CIRCUITSTATE/AQEYE-SB-D1/Export/R0.1/2025-06-06/Renders/AQEYE-SB-D1-R0.1-PCB-Left-06062025-1.png

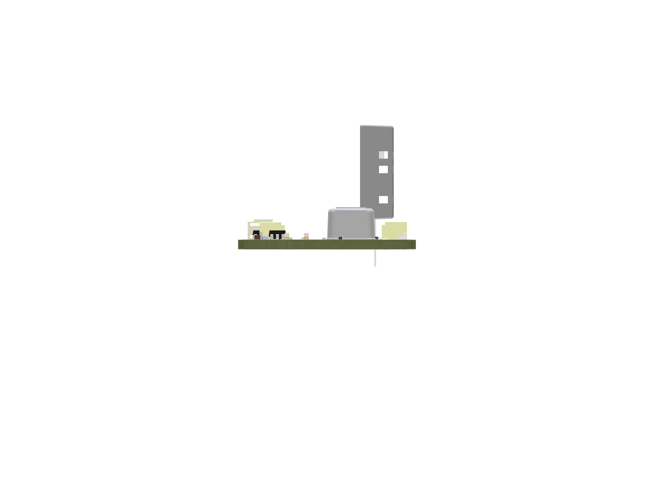
Export/R0.1/2025-06-06/Renders/AQEYE-SB-D1-R0.1-PCB-Left-06062025-1.png
