CIRCUITSTATE/AQEYE-SB-D1/References/sensors_SGP40_sch.png

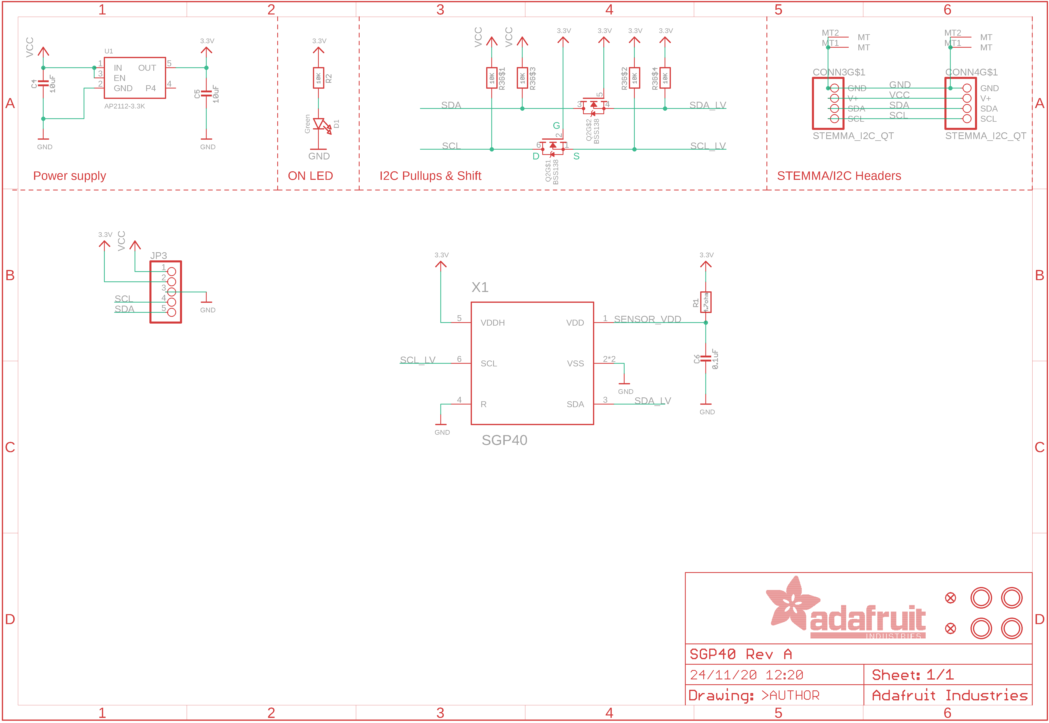
References/sensors_SGP40_sch.png
