CIRCUITSTATE/AQEYE-SB-D1/Export/R0.1/2025-06-08/SCH/AQEYE-SB-D1-R0.1-SCH-08062025-1.pdf

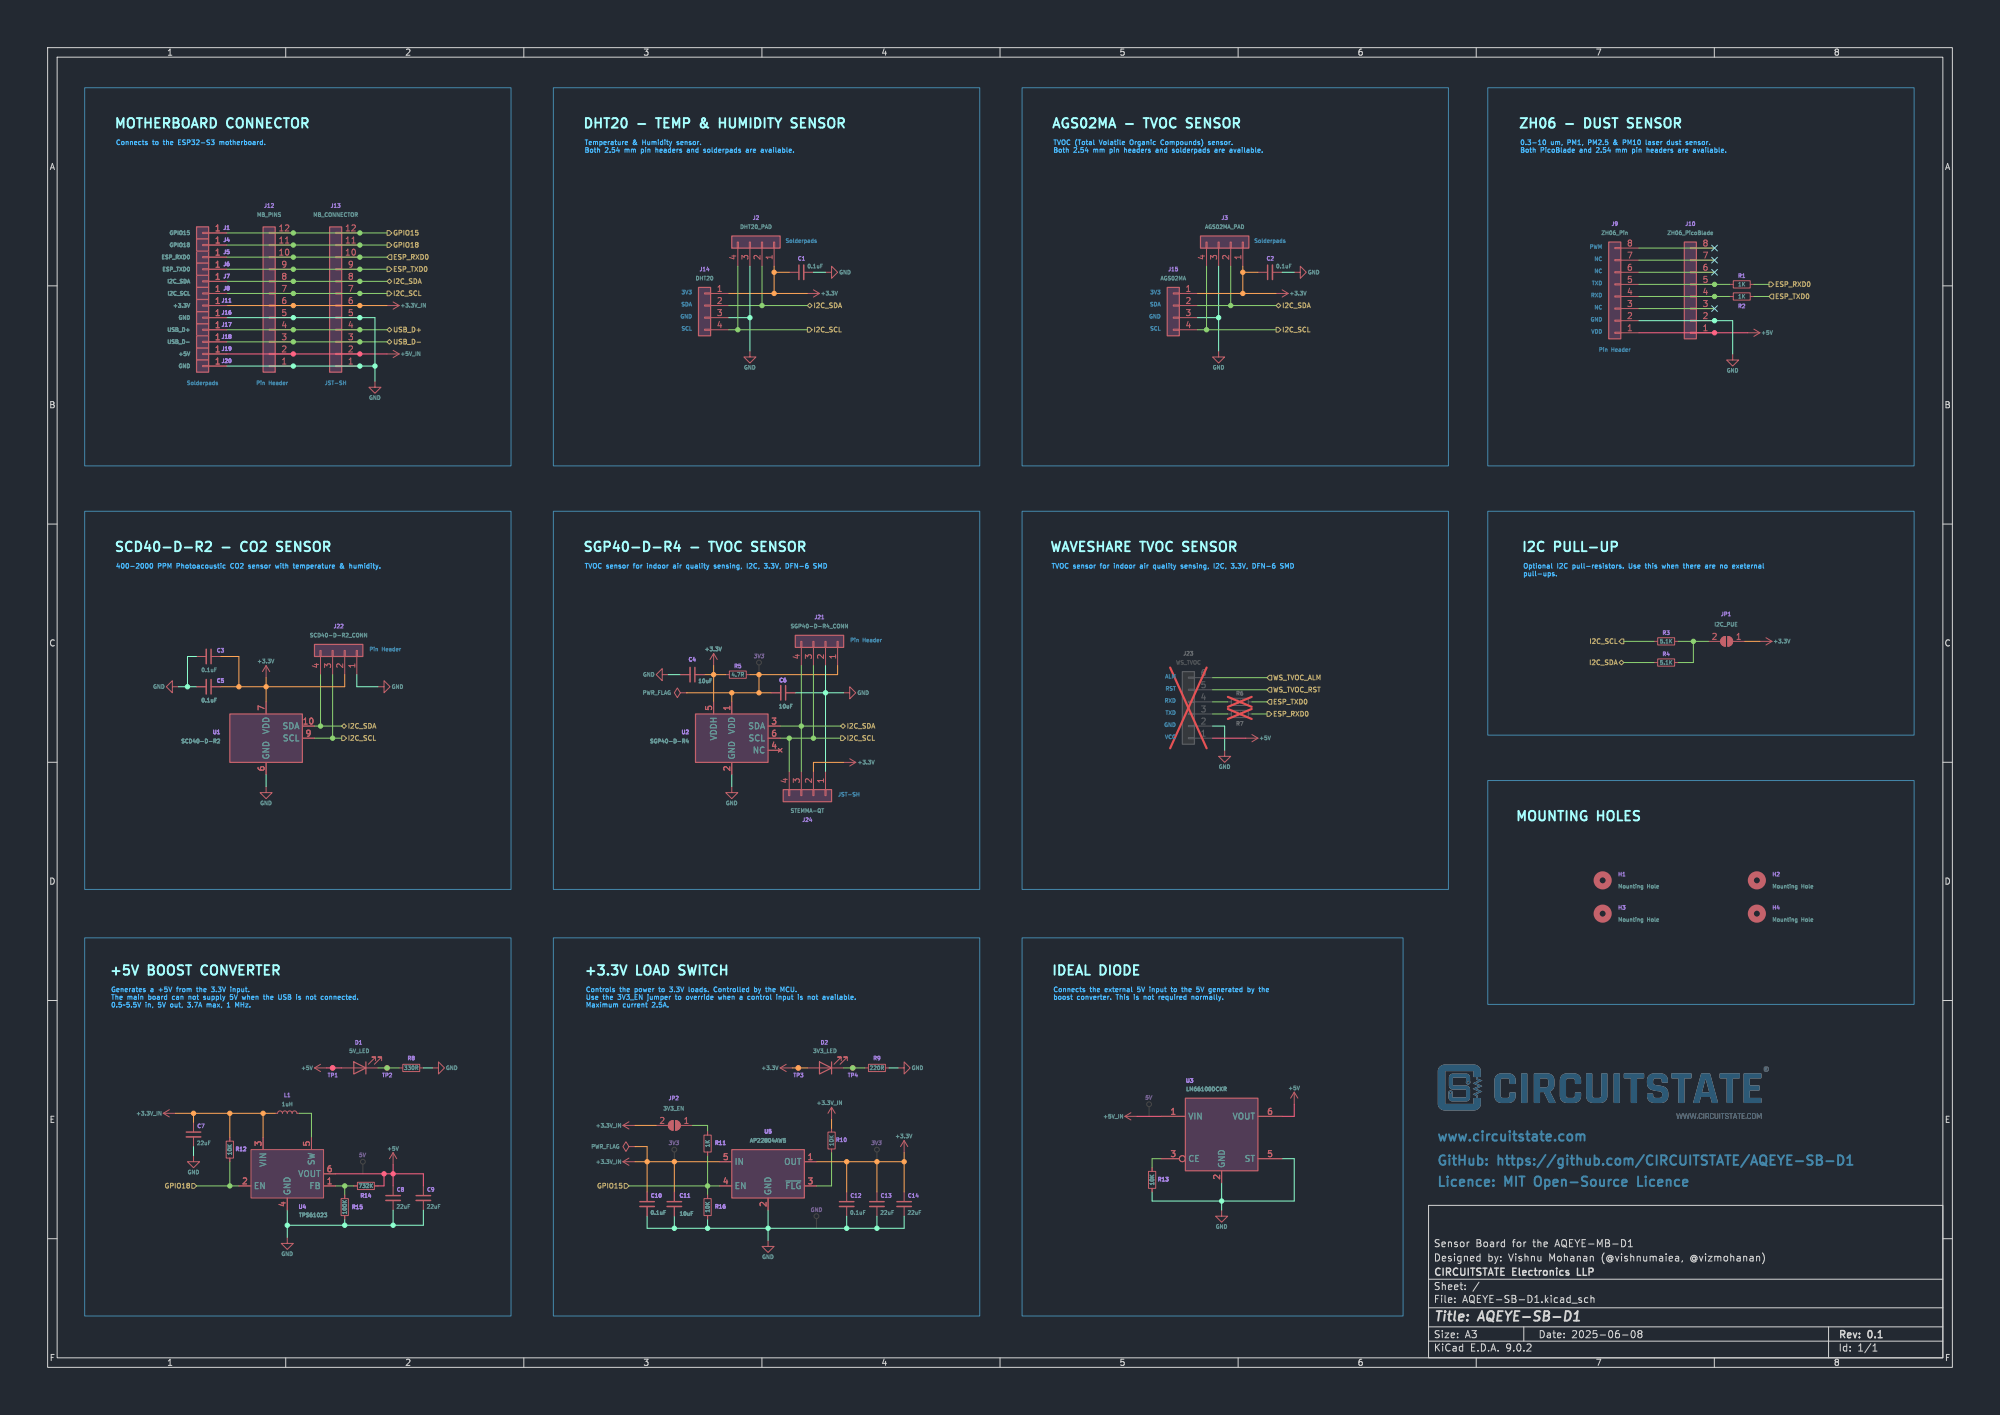
[picture p25: page 1]

RST WAVESHARE TVOC SENSOR

Generates a +5V from the 3.3V input. The main board can not supply 5V when the USB is not connected. 0.5~5.5V in, 5V out, 3.7A max, 1 MHz.

GitHub: https://github.com/CIRCUITSTATE/AQEYE-SB-D1 (https://github.com/CIRCUITSTATE/ESPNut-D1)

Id: 1/1 Title: AQEYE-SB-D1
