CIRCUITSTATE/AQEYE-SB-D1/Export/R0.1/2025-06-06/PCB/AQEYE-SB-D1-R0.1-PCB-PDF-All-06062025-1.pdf

D Date: 2025-06-05 KiCad; E.D.A. 9.0.2 Size: A4; Rev: 0.1; File: AQEYE-SB-D1.kicad_pcb Sheet: CIRCUITSTATE; Electronics; LLP Designed; by: Vishnu; Mohanan (@vishnumaiea,; @vizmohanan) Sensor Board; for the AQEYE-MB-D1

Id: 1/1 Title: AQEYE-SB-D1

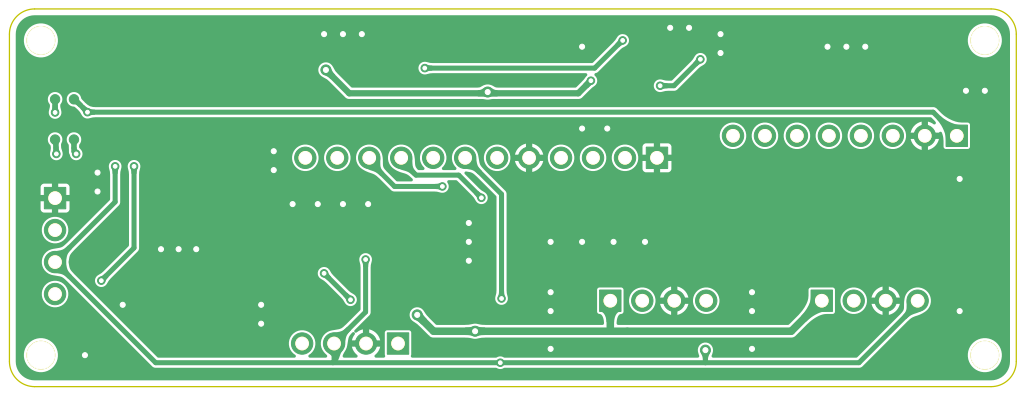
[picture p26: page 2]
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

Id: 1/1 Title: AQEYE-SB-D1

D Date: 2025-06-05 KiCad; E.D.A. 9.0.2 Size: A4; Rev: 0.1; File: AQEYE-SB-D1.kicad_pcb Sheet: CIRCUITSTATE; Electronics; LLP Designed; by: Vishnu; Mohanan (@vishnumaiea,; @vizmohanan) Sensor Board; for the AQEYE-MB-D1; 5V_LED_P; 3V3_LED_P; 5V_LED_M; 3V3_LED_M

Id: 1/1 Title: AQEYE-SB-D1

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

Id: 1/1 Title: AQEYE-SB-D1

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

Id: 1/1 Title: AQEYE-SB-D1

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

Id: 1/1 Title: AQEYE-SB-D1

Id: 1/1 Title: AQEYE-SB-D1

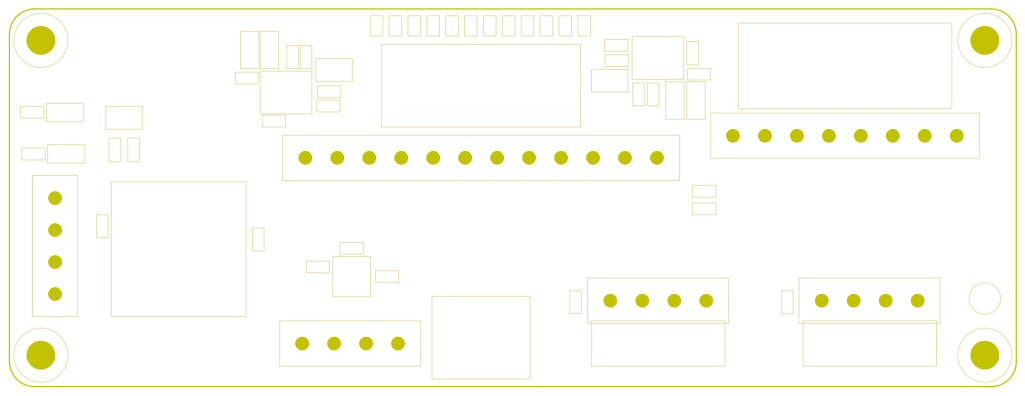
[picture p27: page 8]
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

Id: 1/1 Title: AQEYE-SB-D1

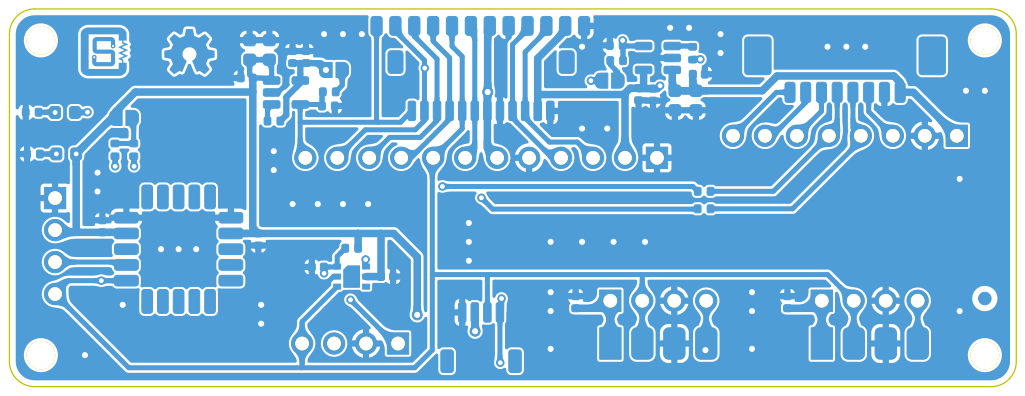
[picture p28: page 9]
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

Id: 1/1 Title: AQEYE-SB-D1

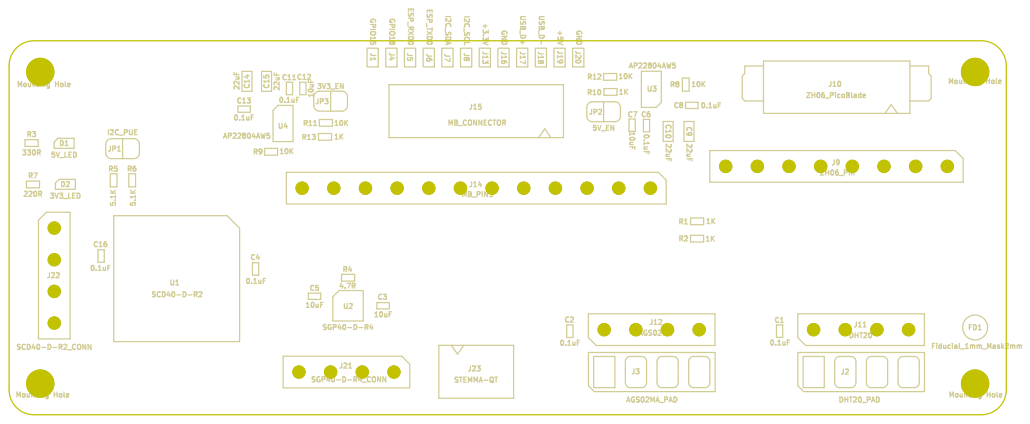
[picture p29: page 10]

Id: 1/1 Title: AQEYE-SB-D1

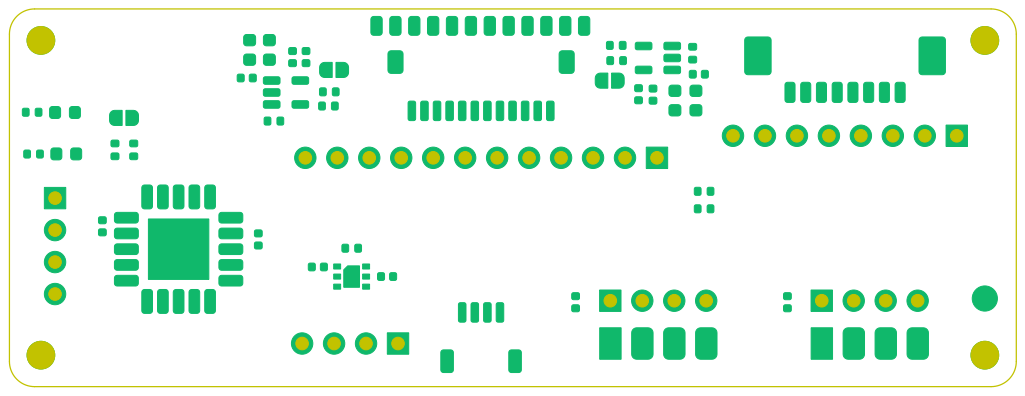
[picture p30: page 11]
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

Id: 1/1 Title: AQEYE-SB-D1

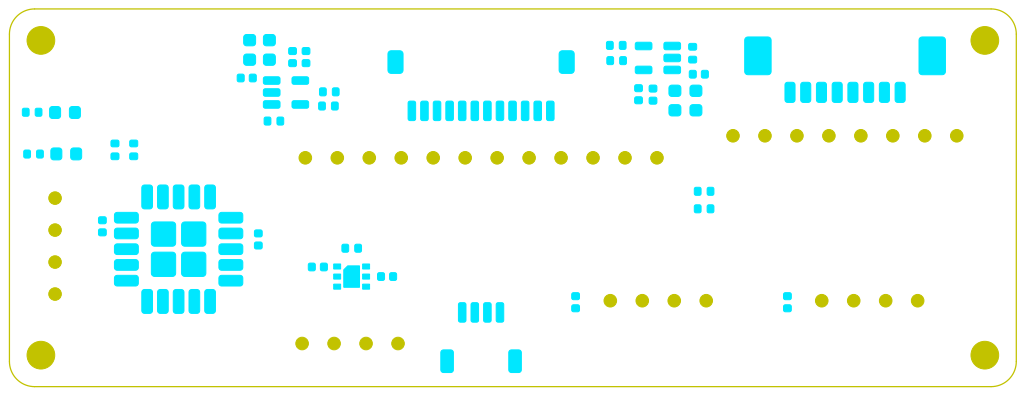
[picture p31: page 12]
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

Id: 1/1 Title: AQEYE-SB-D1

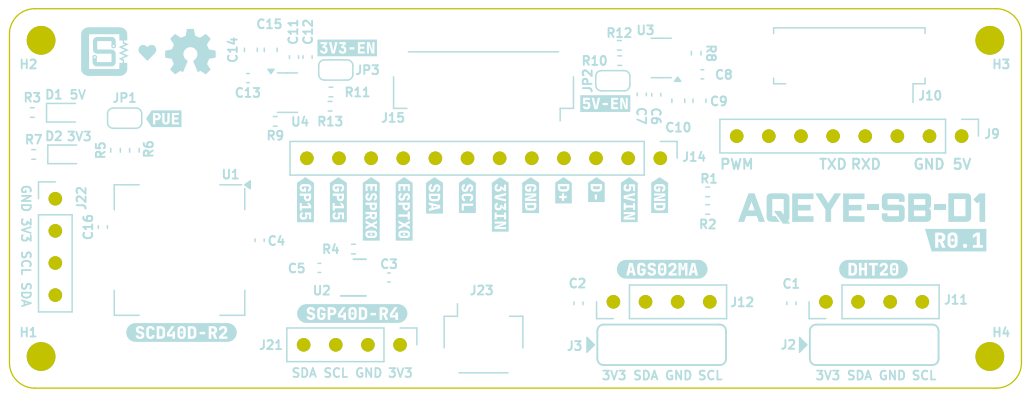
[picture p32: page 13]

Id: 1/1 Title: AQEYE-SB-D1

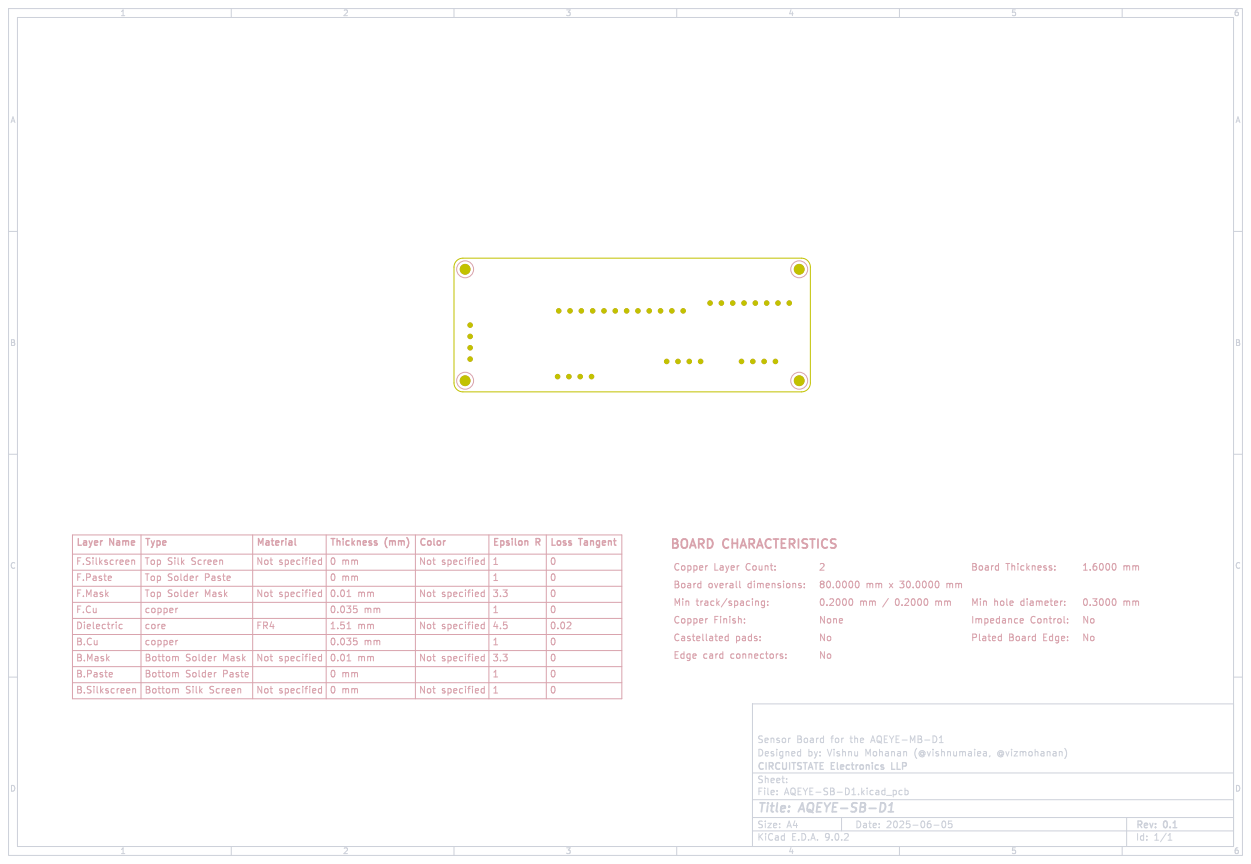
[picture p33: page 14]
D Date: 2025-06-05 KiCad; E.D.A. 9.0.2 Size: A4; Rev: 0.1; File: AQEYE-SB-D1.kicad_pcb Sheet: CIRCUITSTATE; Electronics; LLP Designed; by: Vishnu; Mohanan (@vishnumaiea,; @vizmohanan) Sensor Board; for the AQEYE-MB-D1; copper; Plated; Board; Edge: Not specified; No F.Mask; core; Edge card; connectors: Not specified; Thickness: F.Silkscreen; Bottom Solder Mask; Impedance; Control: Copper; Layer Count: 0; None Thickness; Castellated; pads: Bottom Silk; Screen Dielectric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

Layer Name

Not specified | 1 | 0 0 | No Not specified B.Cu No Type

0 mm | | | | | 0 | 2 Color Not specified Bottom Solder Paste Top Solder Paste

Material | 0 mm | | 1Epsilon R | Loss Tangent Not specified

0.01 mm | 3.3
0 mm

B.Silkscreen | 0 mm | | 0

Id: 1/1 Title: AQEYE-SB-D1

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

Id: 1/1 Title: AQEYE-SB-D1
