CIRCUITSTATE/AQEYE-SB-D1/Export/R0.1/2025-06-06/SCH/AQEYE-SB-D1-R0.1-SCH-06062025-1.pdf

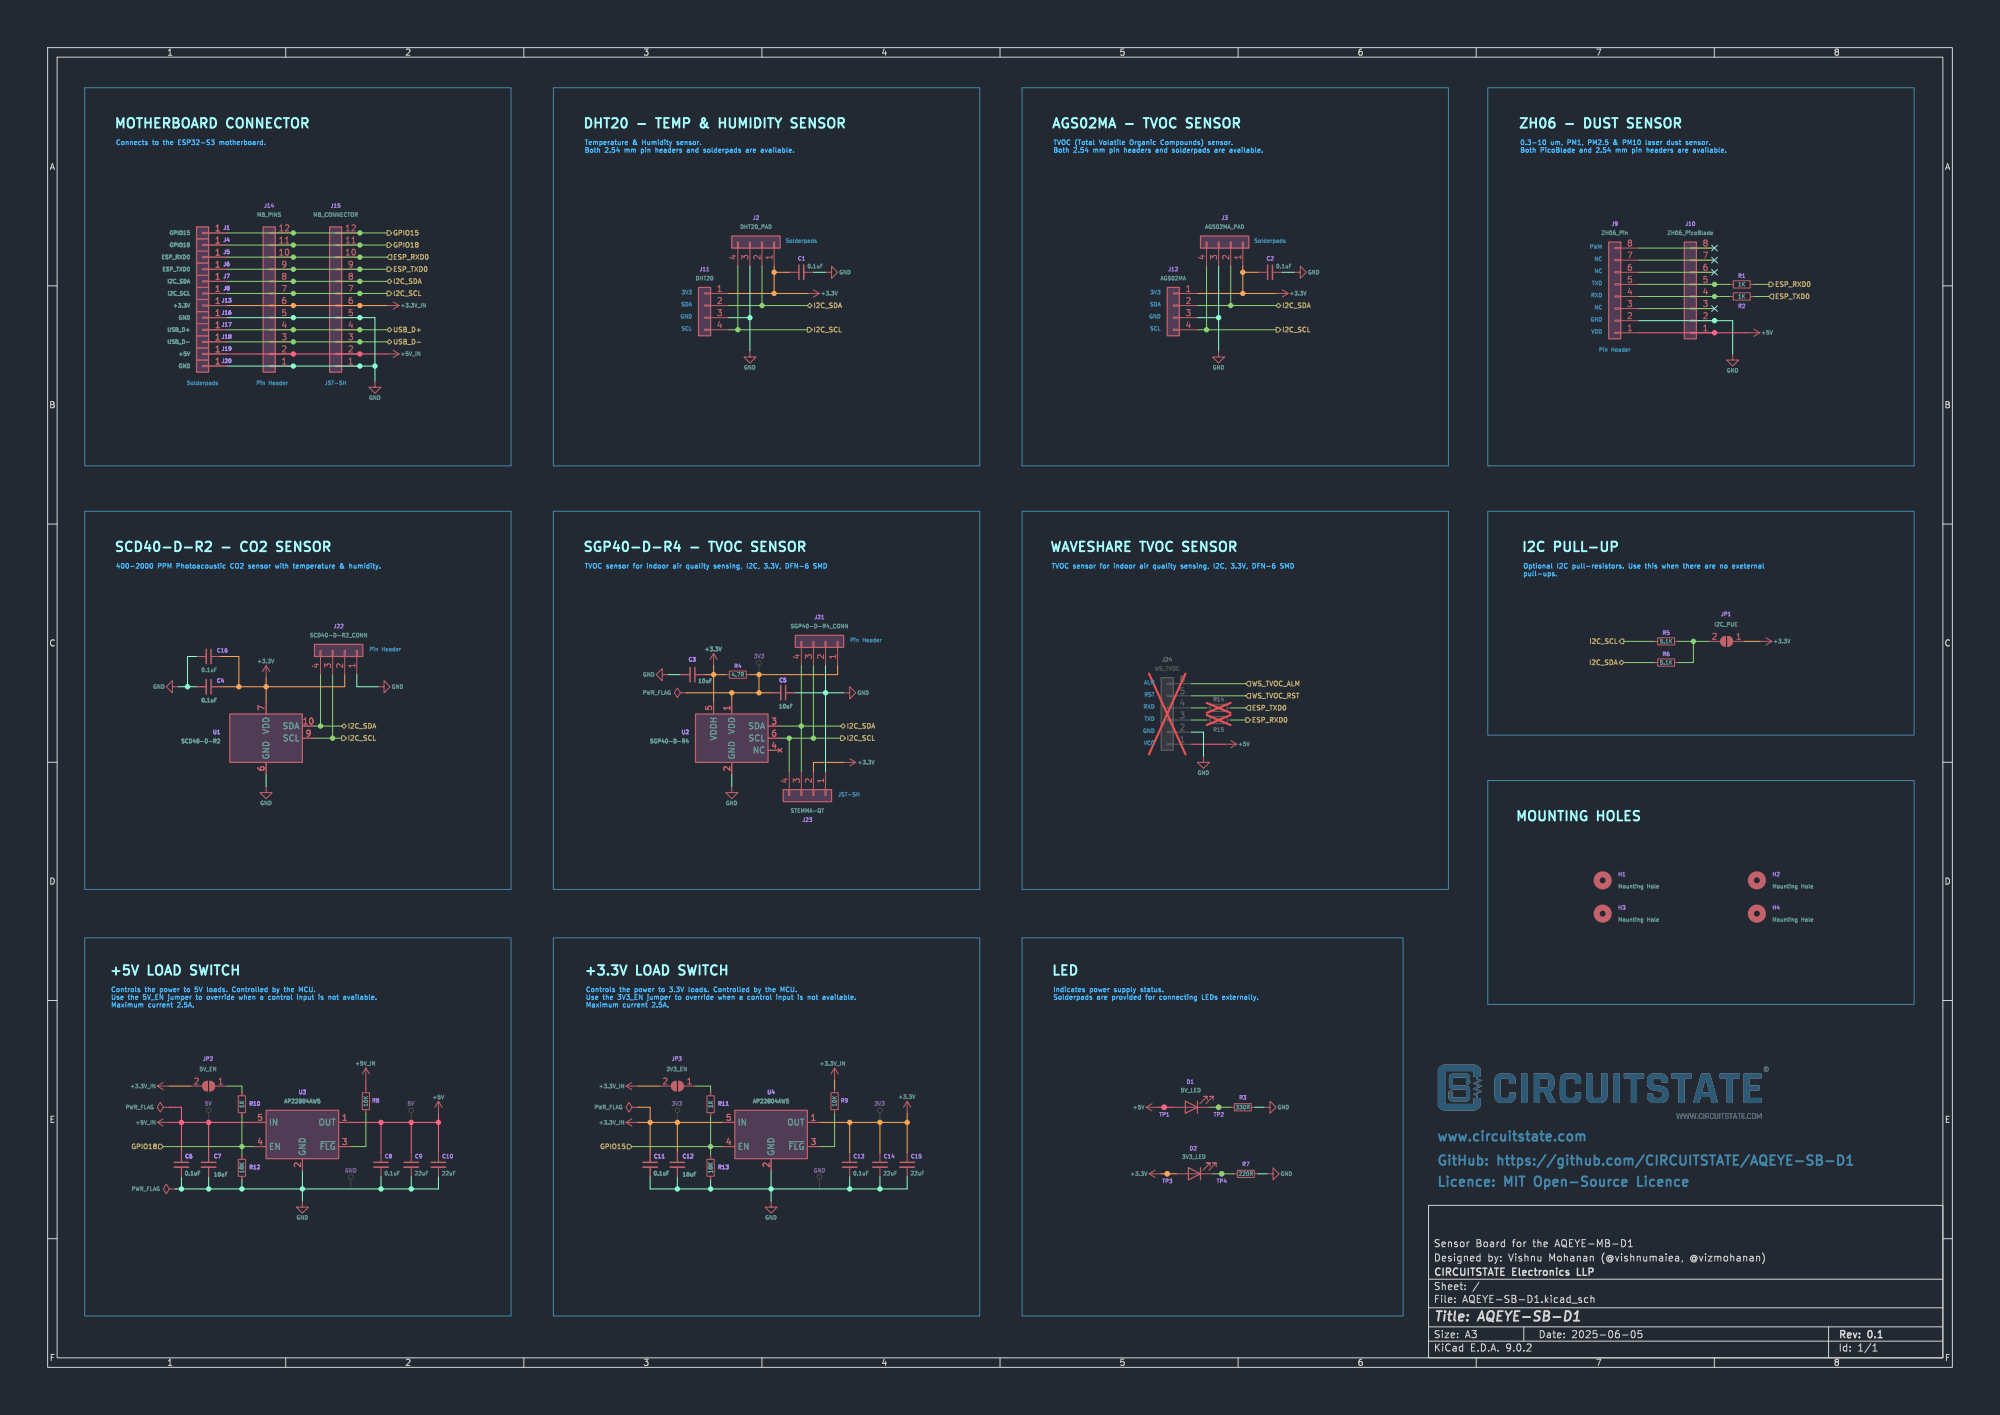
[picture p34: page 1]

Solderpads DHT20 - TEMP & HUMIDITY SENSOR

Pin Header

VCC GND WAVESHARE TVOC SENSOR

GitHub: https://github.com/CIRCUITSTATE/AQEYE-SB-D1 (https://github.com/CIRCUITSTATE/ESPNut-D1)

Id: 1/1 Title: AQEYE-SB-D1
