CIRCUITSTATE/AQEYE-SB-D1/Export/R0.1/2025-06-08/PCB/AQEYE-SB-D1-R0.1-User_Drawings.pdf

Id: 1/1 Title: AQEYE-SB-D1
