CIRCUITSTATE/AQEYE-SB-D1/Export/R0.1/2025-06-06/PCB/AQEYE-SB-D1-R0.1-Edge_Cuts.pdf

Id: 1/1 Title: AQEYE-SB-D1
